zaeem7744/TapBand-Firmware-and-PCB/MQTT/MQTT.ino

#include <WiFi.h>
#include <PubSubClient.h>

/* WiFi credentials */
const char* ssid = "VAASA-65200"                                                                                                                                                                                                                                                                                                                                                                                                                                                                                                                                                                                                                                                                                                                                                                                                                                                                                                                                                                                                                                                                                                                                                                                                                                                                                                                                                                                                                                                                                                                            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
const char* password = "01234567890";

/* MQTT settings */
const char* mqtt_server = "broker.hivemq.com";  // Public MQTT broker
const int mqtt_port = 1883;
const char* subscribe_topic = "test/topic";
const char* publish_topic = "test/topic";

WiFiClient espClient;
PubSubClient client(espClient);

void callback(char* topic, byte* payload, unsigned int length) {
  Serial.print("Message on [");
  Serial.print(topic);
  Serial.print("]: ");
  for (int i = 0; i < length; i++) Serial.print((char)payload[i]);
  Serial.println();
}

void connectMQTT() {
  while (!client.connected()) {
    Serial.print("Connecting to MQTT...");
    if (client.connect("esp32-client-id")) {
      Serial.println("connected");
      client.subscribe(subscribe_topic);
    } else {
      Serial.print("failed, rc=");
      Serial.print(client.state());
      delay(2000);
    }
  }
}

void setup() {
  Serial.begin(115200);

  WiFi.begin(ssid, password);
  Serial.print("Connecting to WiFi");
  while (WiFi.status() != WL_CONNECTED) {
    delay(500); Serial.print(".");
  }
  Serial.println(" connected!");

  client.setServer(mqtt_server, mqtt_port);
  client.setCallback(callback);
}

void loop() {
  if (!client.connected()) connectMQTT();
  client.loop();

  // Publish every 5 seconds
  static unsigned long lastTime = 0;
  if (millis() - lastTime > 5000) {
    lastTime = millis();
    client.publish(publish_topic, "ESP32 says hi!");
    Serial.println("Message published");
  }
}
